thegavs/openhab-trains/arduino modules/signal levers/levers/cobolt.jpg

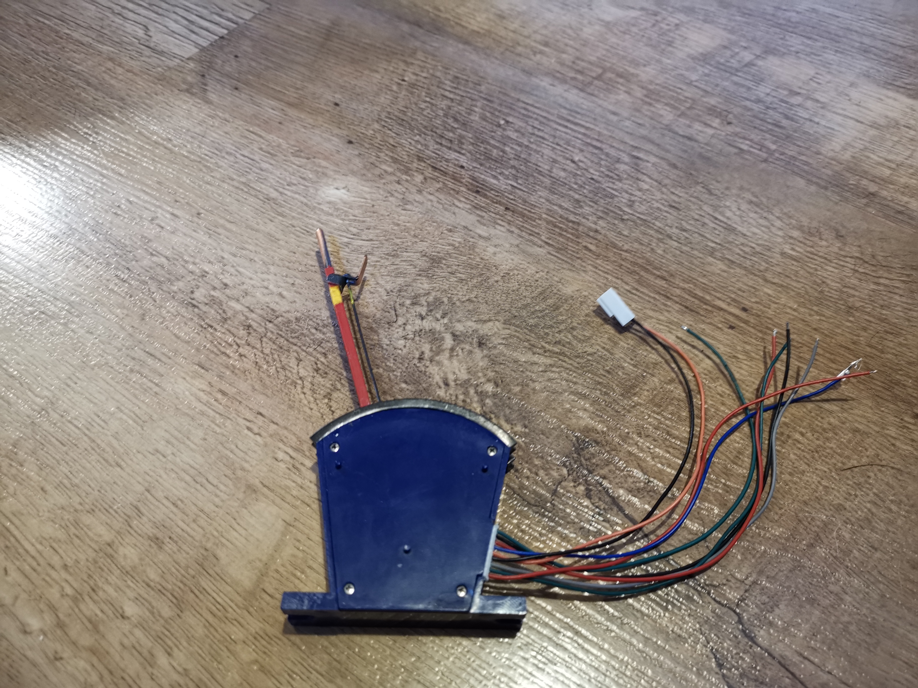
arduino modules/signal levers/levers/cobolt.jpg
