thegavs/openhab-trains/arduino modules/signal levers/levers/levers.png

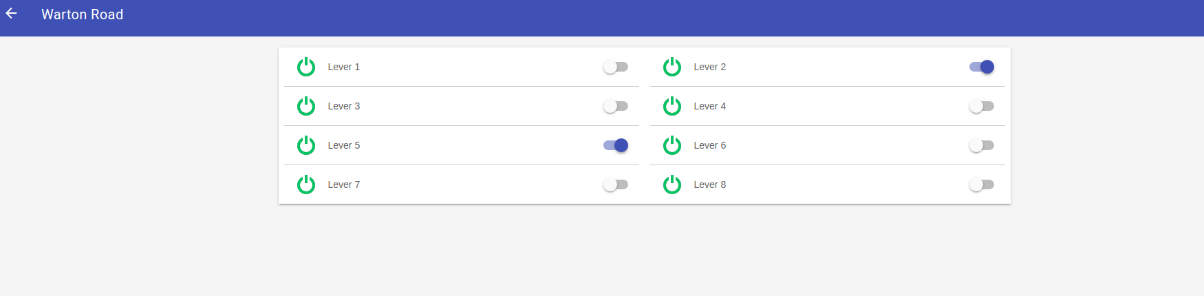
arduino modules/signal levers/levers/levers.png
