thegavs/openhab-trains/arduino modules/signal levers/levers/map transformation.png

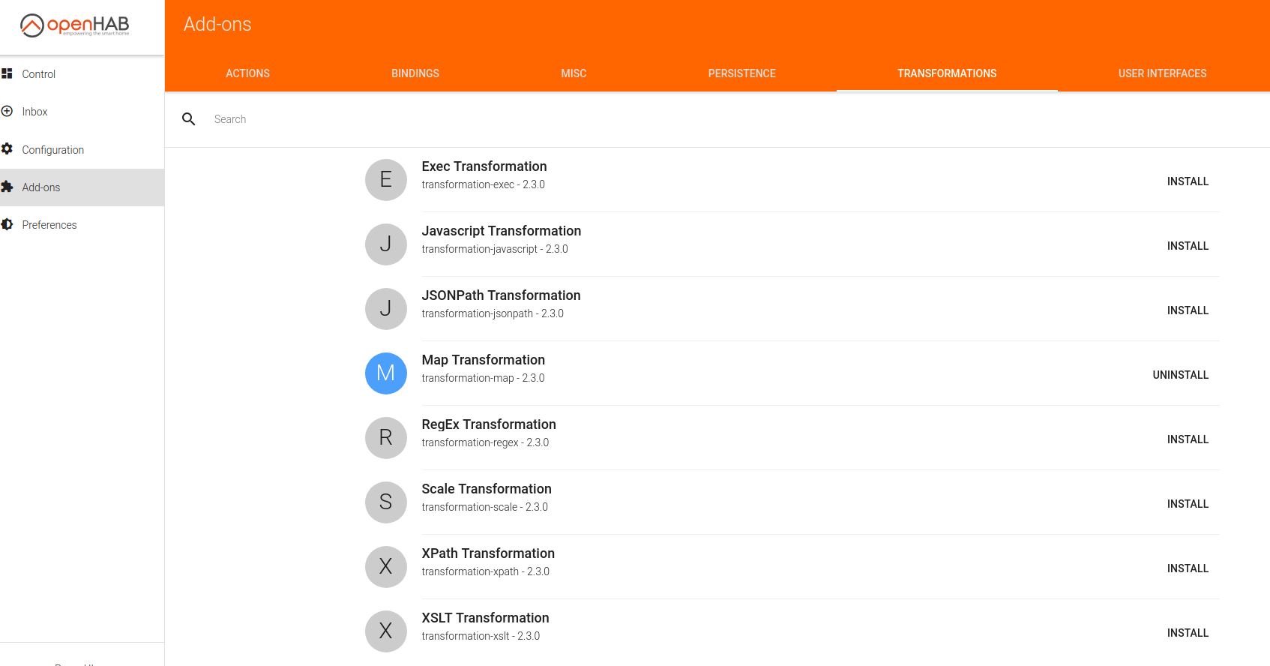
arduino modules/signal levers/levers/map transformation.png
